DF3MT/esp32-flrig/include/web_config.h

#pragma once

#include "config.h"
#include <functional>

class RadioChannelManager;

class WebConfig {
public:
    using SaveCallback = std::function<void(const AppConfig&)>;

    bool begin(AppConfig* cfg, SaveCallback onSave);
    void attachRadioAudio(RadioChannelManager* radios);
    void loop();

private:
    AppConfig* _cfg = nullptr;
    SaveCallback _onSave;
};
